YoussefMadian/safe-driving-system/Presentation/Photos/Slide1.JPG

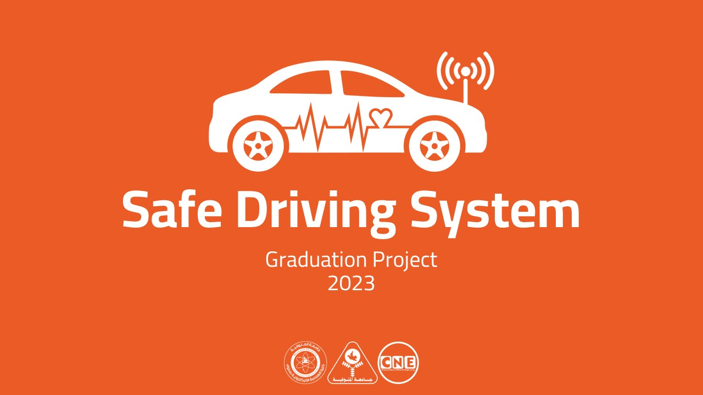
Presentation/Photos/Slide1.JPG
