YoussefMadian/safe-driving-system/Presentation/Photos/Slide2.JPG

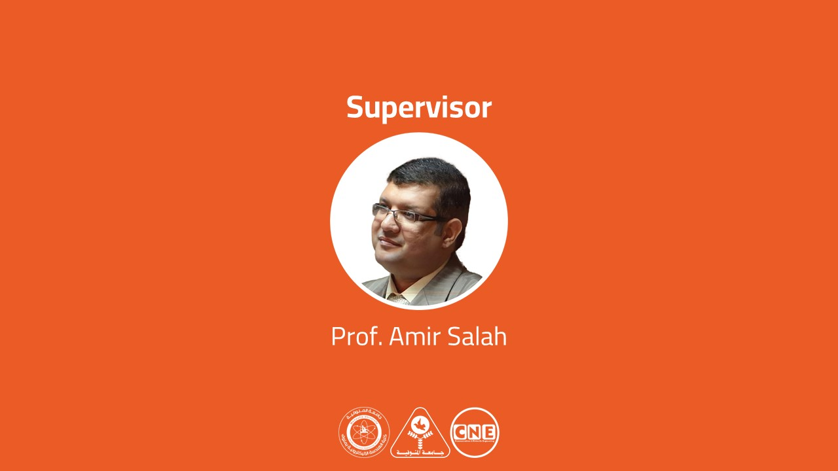
Presentation/Photos/Slide2.JPG
