YoussefMadian/safe-driving-system/Presentation/Photos/Slide3.JPG

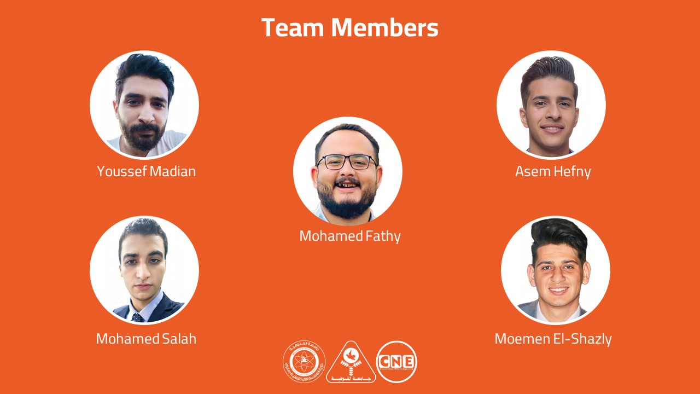
Presentation/Photos/Slide3.JPG
