YoussefMadian/safe-driving-system/Presentation/Photos/Slide4.JPG

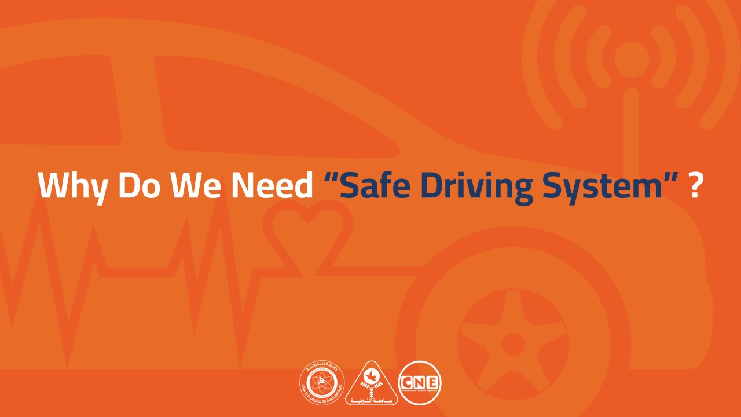
Presentation/Photos/Slide4.JPG
