YoussefMadian/safe-driving-system/Presentation/Photos/Slide5.JPG

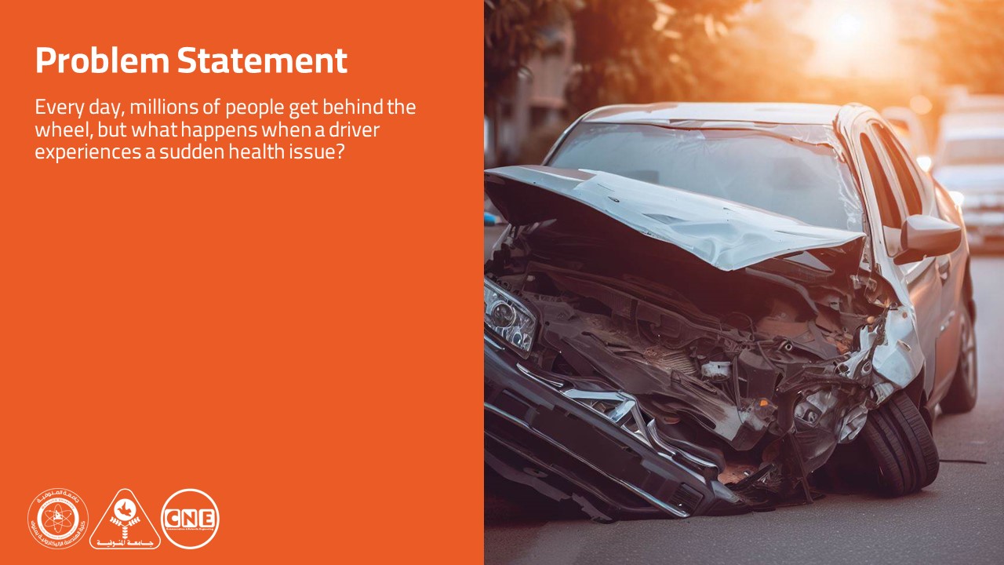
Presentation/Photos/Slide5.JPG
