YoussefMadian/safe-driving-system/Presentation/Photos/Slide6.JPG

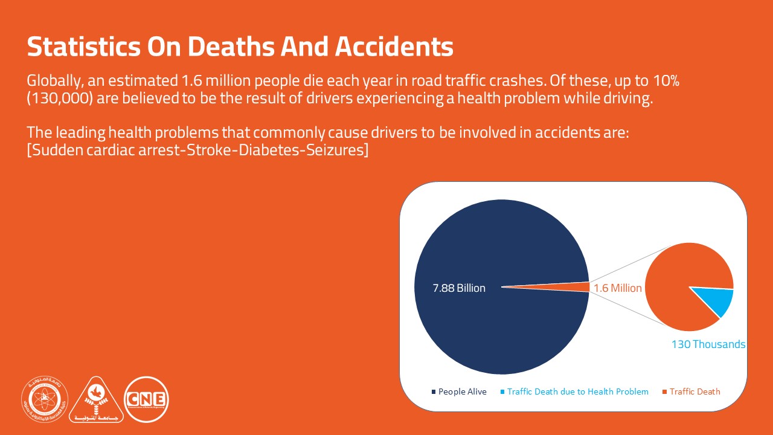
Presentation/Photos/Slide6.JPG
