YoussefMadian/safe-driving-system/Presentation/Photos/Slide7.JPG

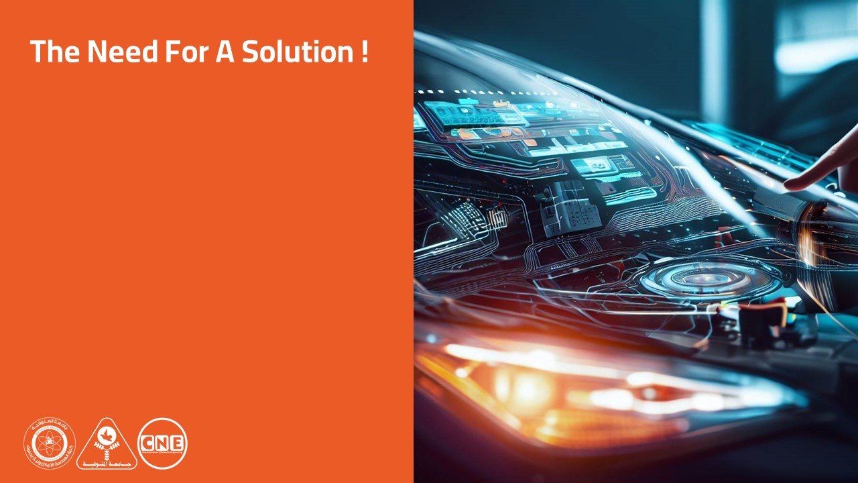
Presentation/Photos/Slide7.JPG
