YoussefMadian/safe-driving-system/Presentation/Photos/Slide8.JPG

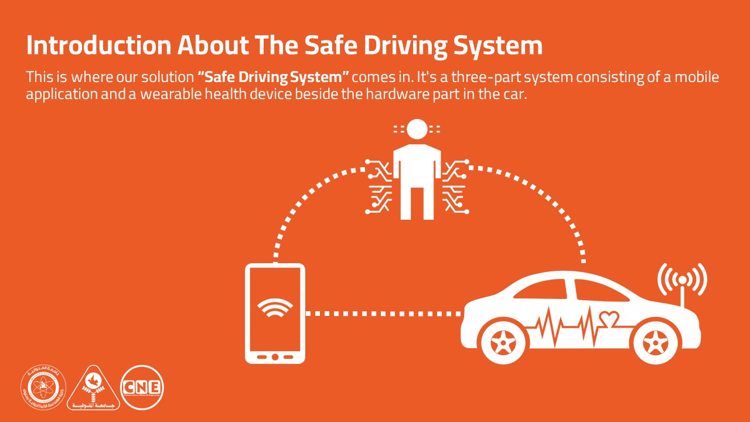
Presentation/Photos/Slide8.JPG
