YoussefMadian/safe-driving-system/Presentation/Photos/Slide9.JPG

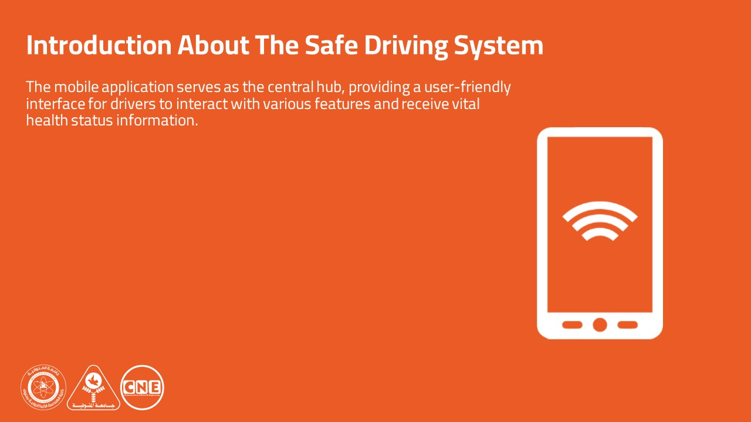
Presentation/Photos/Slide9.JPG
