YoussefMadian/safe-driving-system/Presentation/Photos/Slide10.JPG

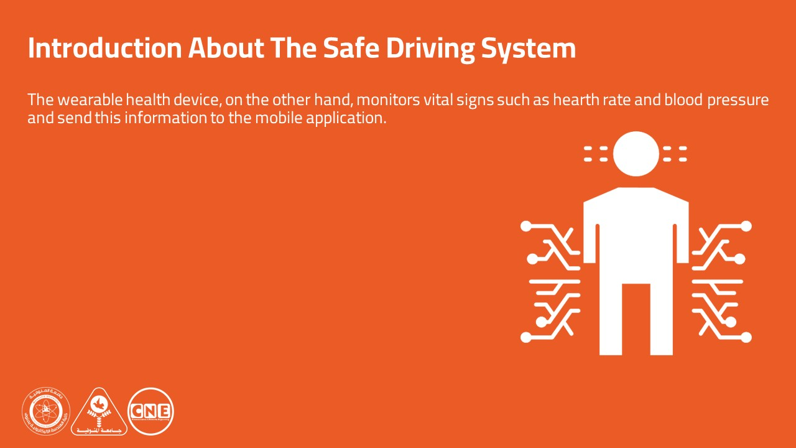
Presentation/Photos/Slide10.JPG
