YoussefMadian/safe-driving-system/Presentation/Photos/Slide11.JPG

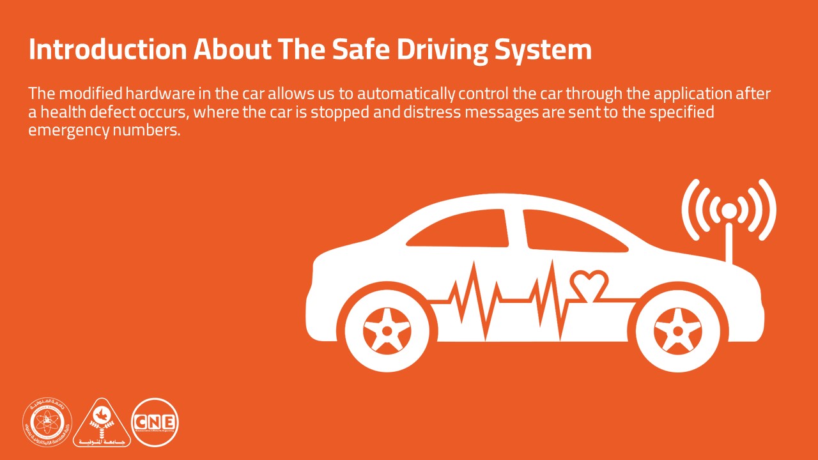
Presentation/Photos/Slide11.JPG
