YoussefMadian/safe-driving-system/Presentation/Photos/Slide12.JPG

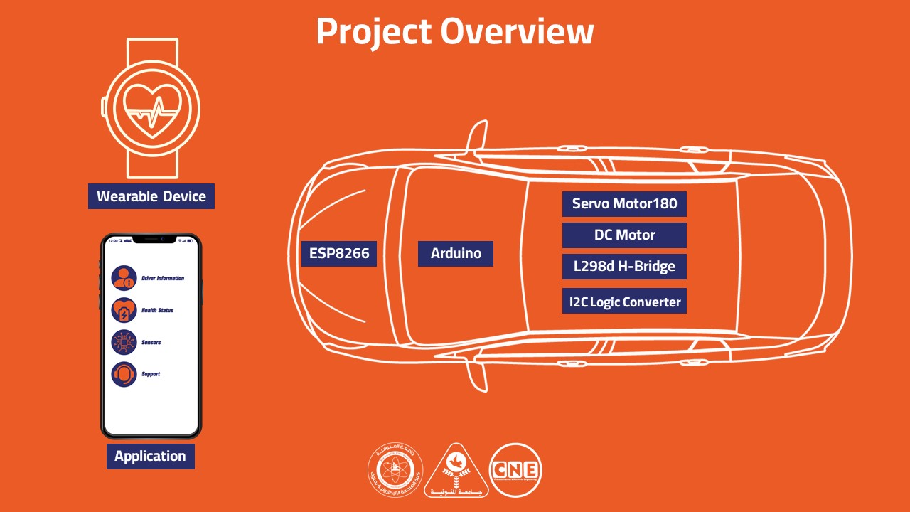
Presentation/Photos/Slide12.JPG
