YoussefMadian/safe-driving-system/Presentation/Photos/Slide13.JPG

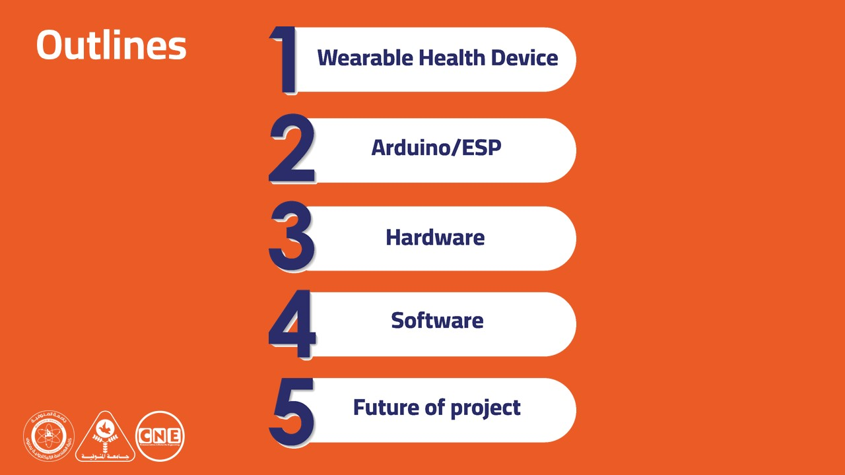
Presentation/Photos/Slide13.JPG
