YoussefMadian/safe-driving-system/Presentation/Photos/Slide14.JPG

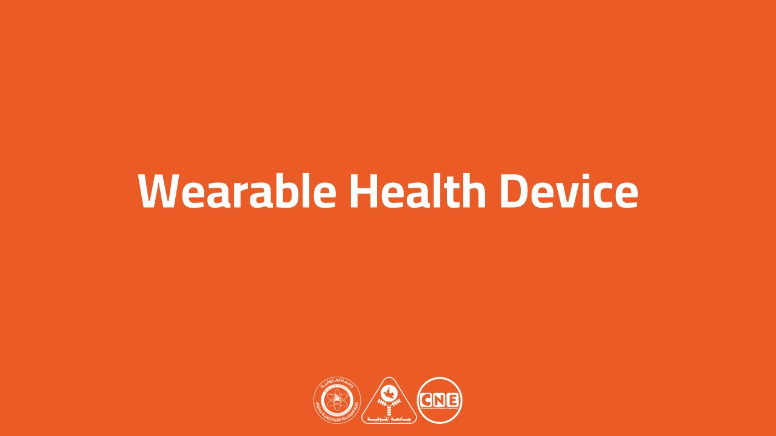
Presentation/Photos/Slide14.JPG
