YoussefMadian/safe-driving-system/Presentation/Photos/Slide15.JPG

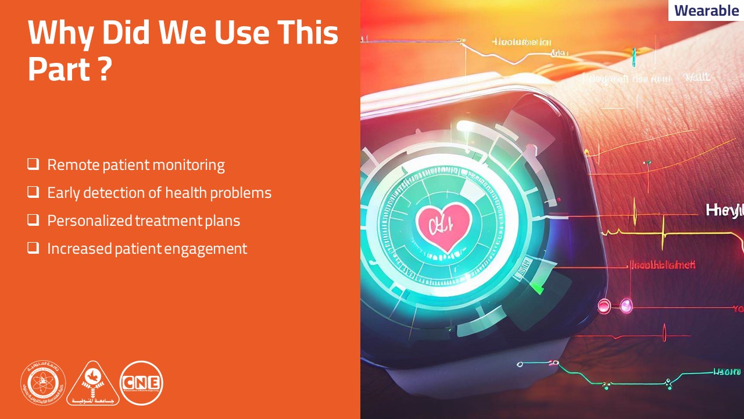
Presentation/Photos/Slide15.JPG
