YoussefMadian/safe-driving-system/Presentation/Photos/Slide16.JPG

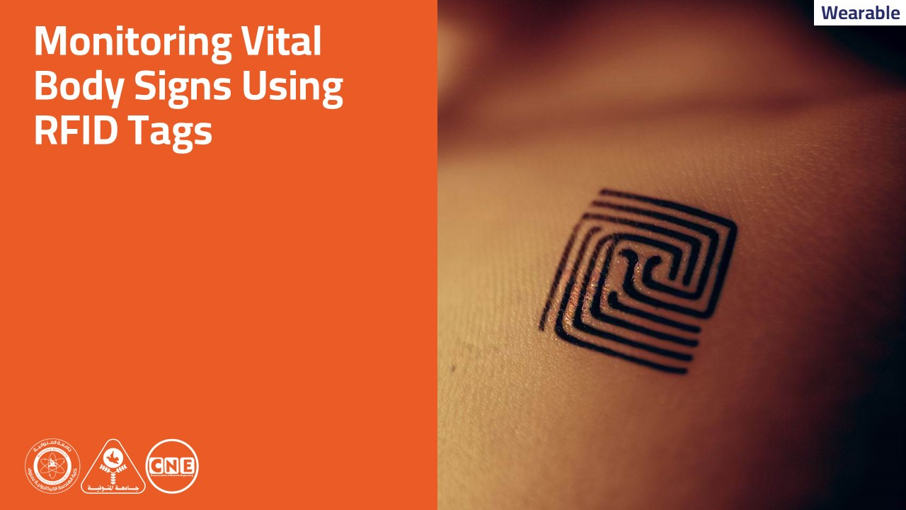
Presentation/Photos/Slide16.JPG
