YoussefMadian/safe-driving-system/Presentation/Photos/Slide18.JPG

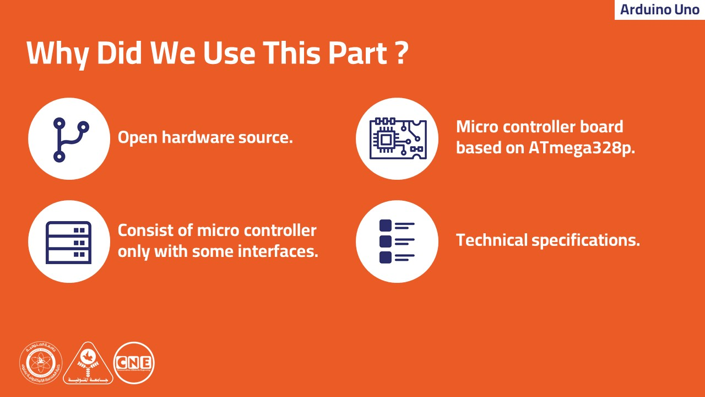
Presentation/Photos/Slide18.JPG
