YoussefMadian/safe-driving-system/Presentation/Photos/Slide19.JPG

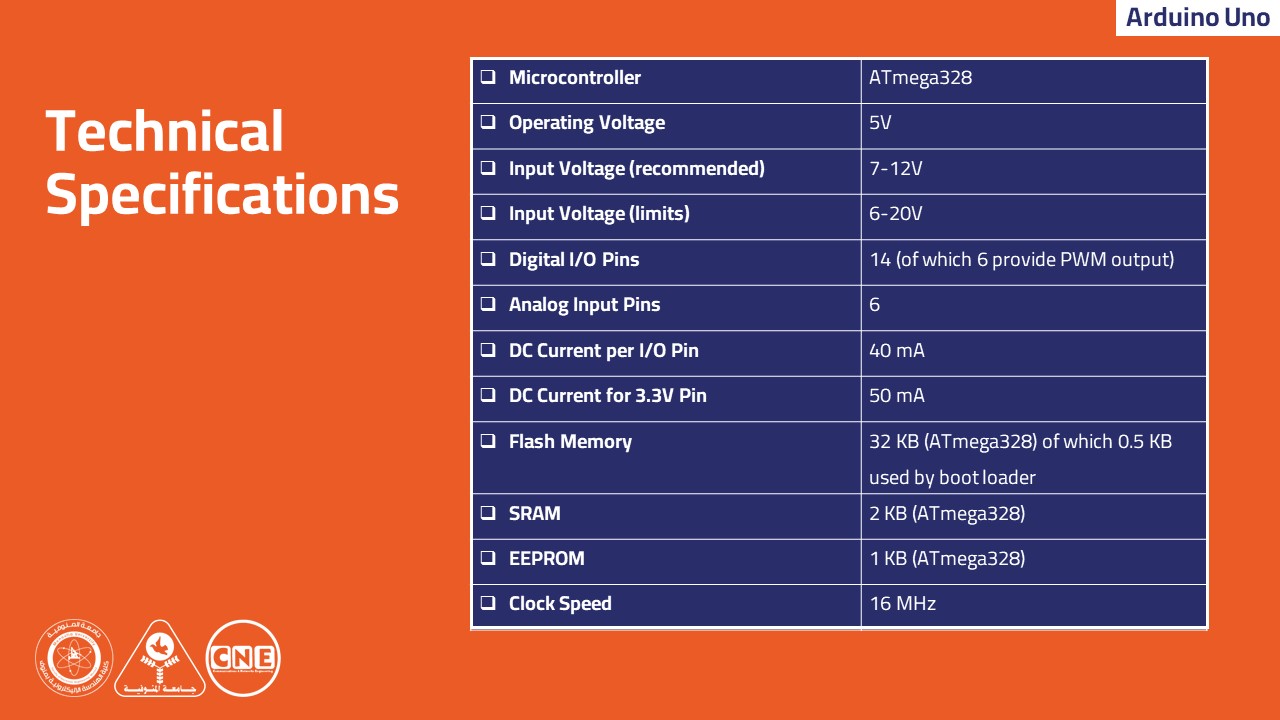
Presentation/Photos/Slide19.JPG
