YoussefMadian/safe-driving-system/Presentation/Photos/Slide20.JPG

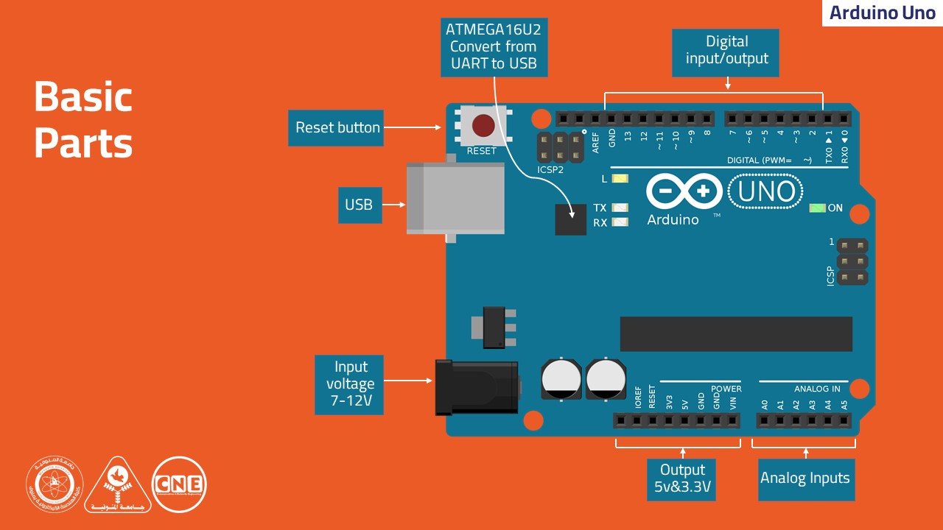
Presentation/Photos/Slide20.JPG
