YoussefMadian/safe-driving-system/Presentation/Photos/Slide22.JPG

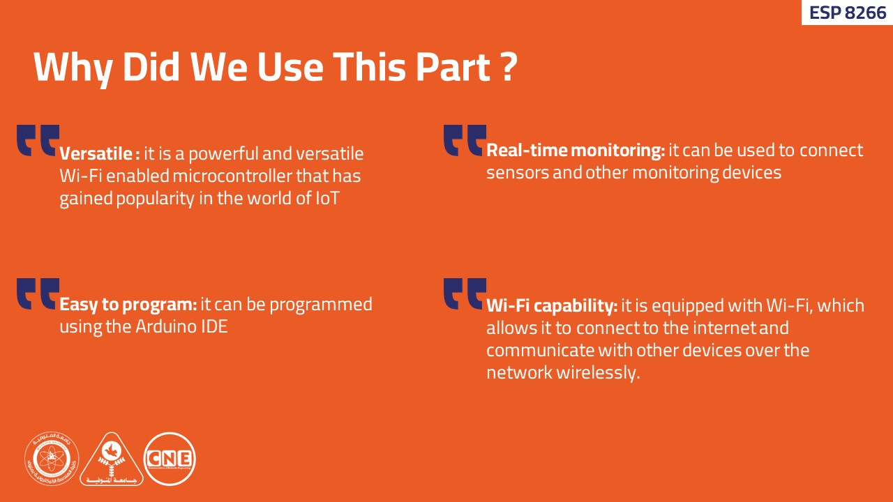
Presentation/Photos/Slide22.JPG
