YoussefMadian/safe-driving-system/Presentation/Photos/Slide23.JPG

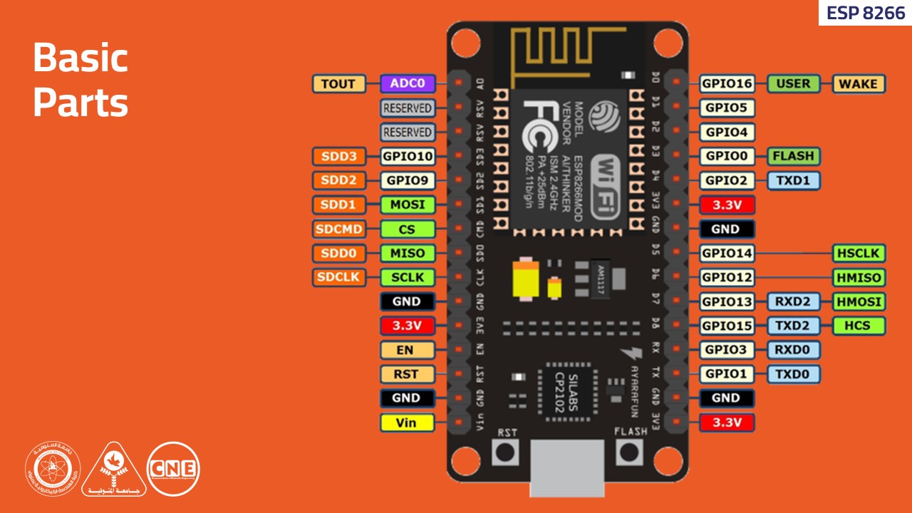
Presentation/Photos/Slide23.JPG
