YoussefMadian/safe-driving-system/Presentation/Photos/Slide24.JPG

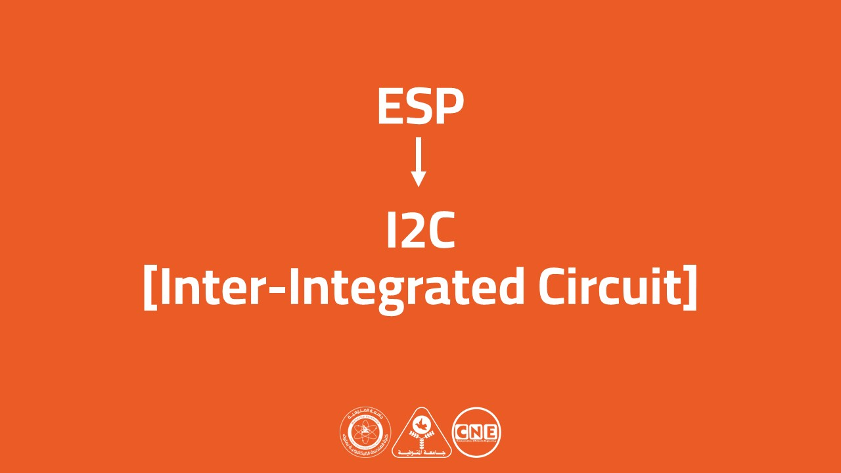
Presentation/Photos/Slide24.JPG
