YoussefMadian/safe-driving-system/Presentation/Photos/Slide25.JPG

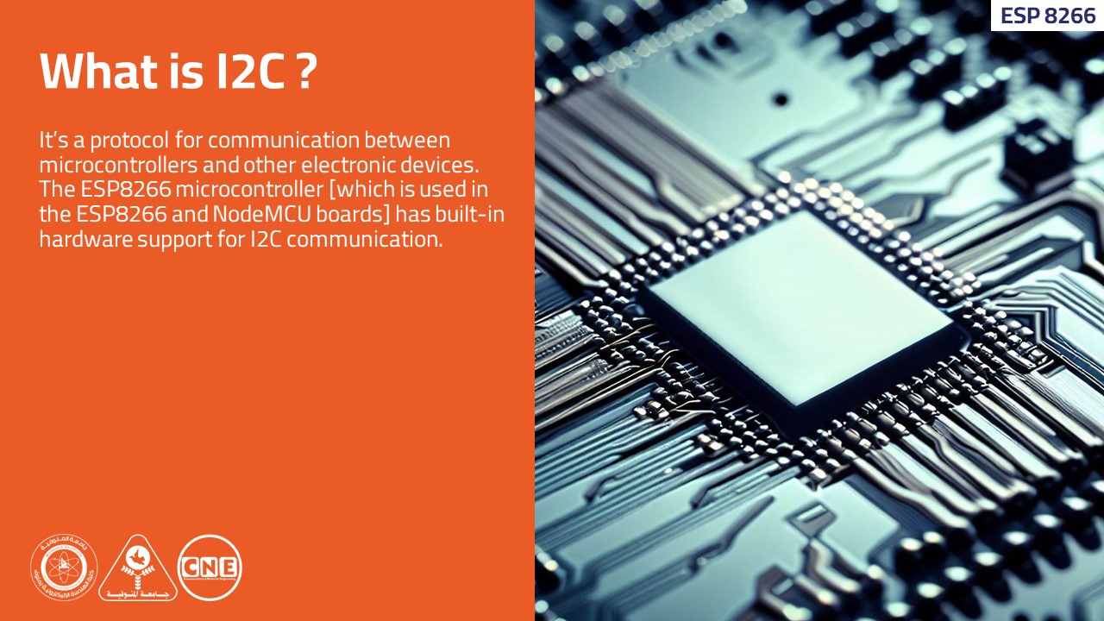
Presentation/Photos/Slide25.JPG
