YoussefMadian/safe-driving-system/Presentation/Photos/Slide26.JPG

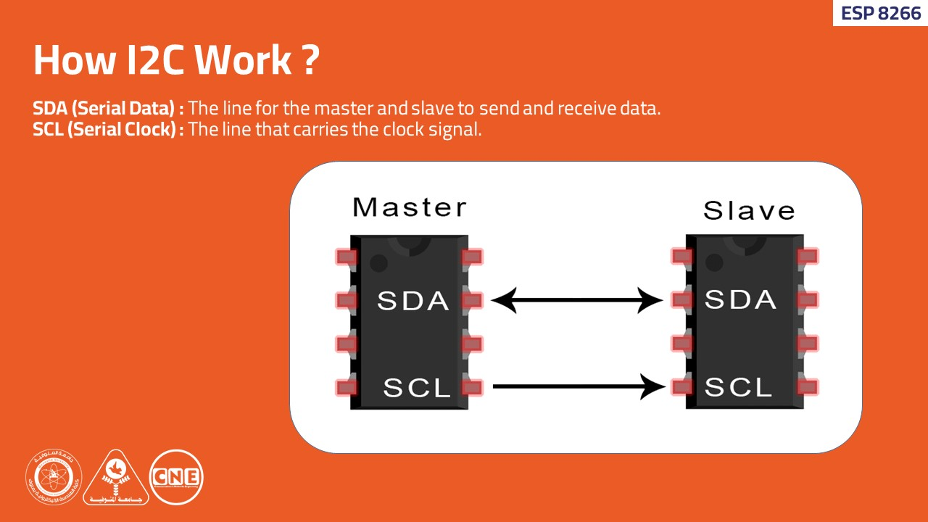
Presentation/Photos/Slide26.JPG
