YoussefMadian/safe-driving-system/Presentation/Photos/Slide27.JPG

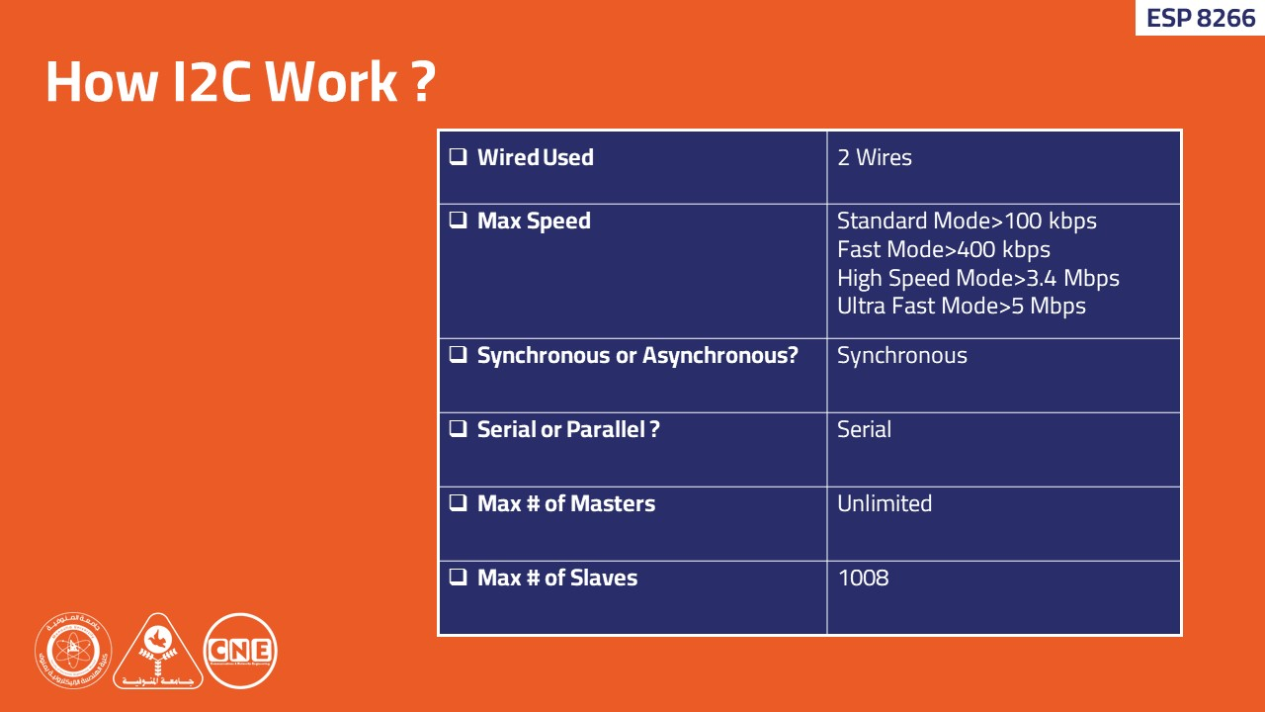
Presentation/Photos/Slide27.JPG
