YoussefMadian/safe-driving-system/Presentation/Photos/Slide28.JPG

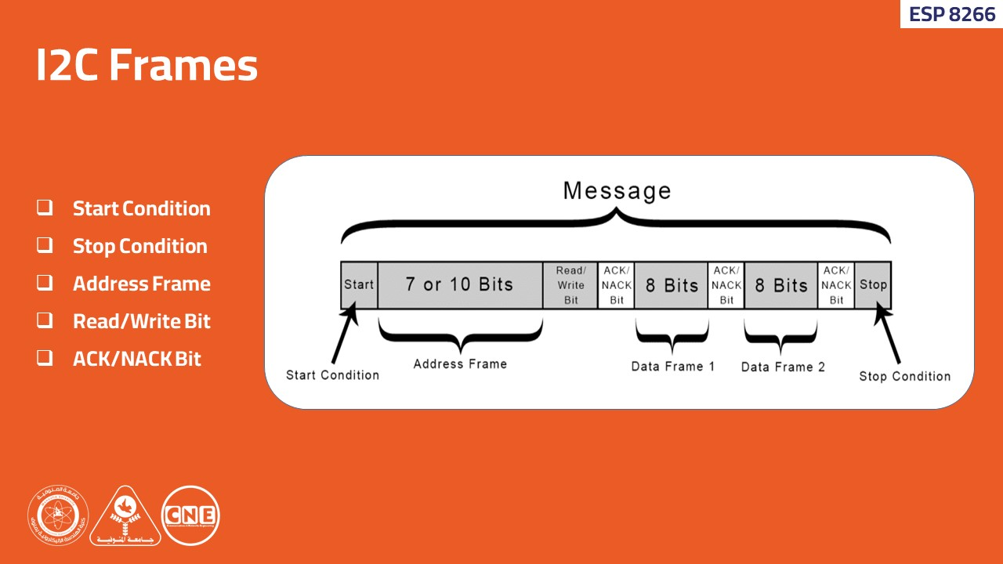
Presentation/Photos/Slide28.JPG
