YoussefMadian/safe-driving-system/Presentation/Photos/Slide29.JPG

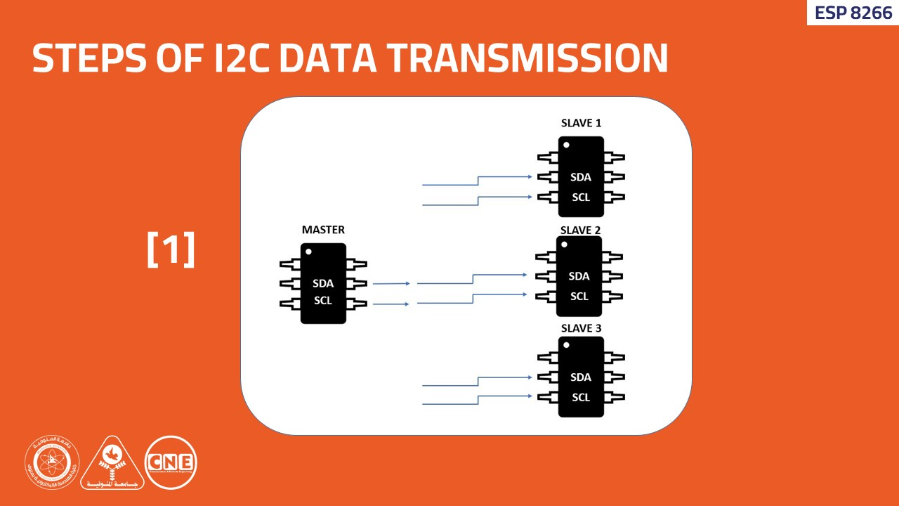
Presentation/Photos/Slide29.JPG
