YoussefMadian/safe-driving-system/Presentation/Photos/Slide33.JPG

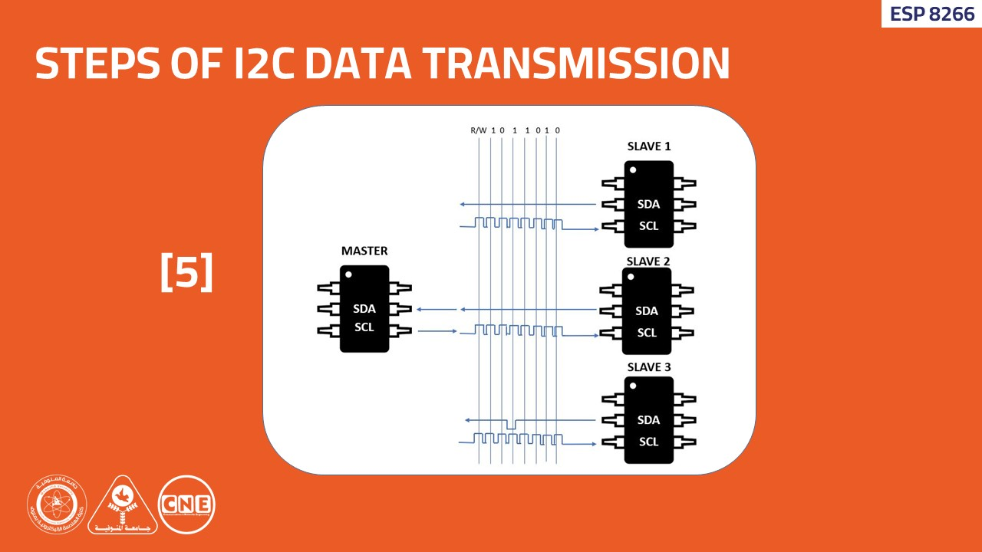
Presentation/Photos/Slide33.JPG
