YoussefMadian/safe-driving-system/Presentation/Photos/Slide35.JPG

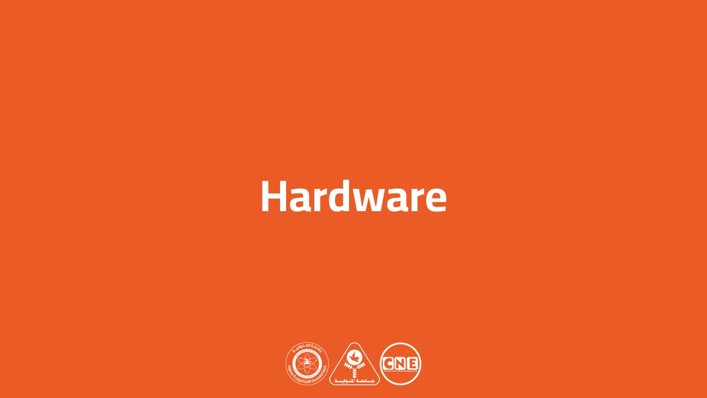
Presentation/Photos/Slide35.JPG
