YoussefMadian/safe-driving-system/Presentation/Photos/Slide36.JPG

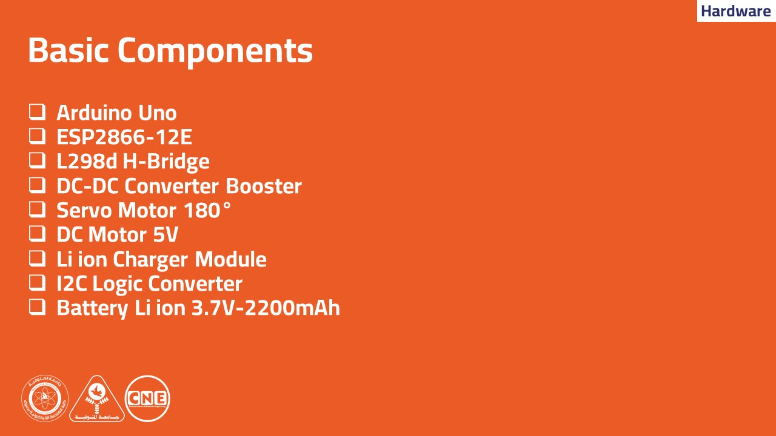
Presentation/Photos/Slide36.JPG
