YoussefMadian/safe-driving-system/Presentation/Photos/Slide37.JPG

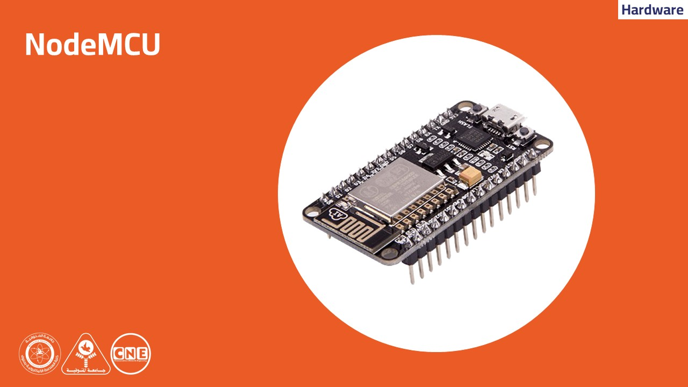
Presentation/Photos/Slide37.JPG
