YoussefMadian/safe-driving-system/Presentation/Photos/Slide38.JPG

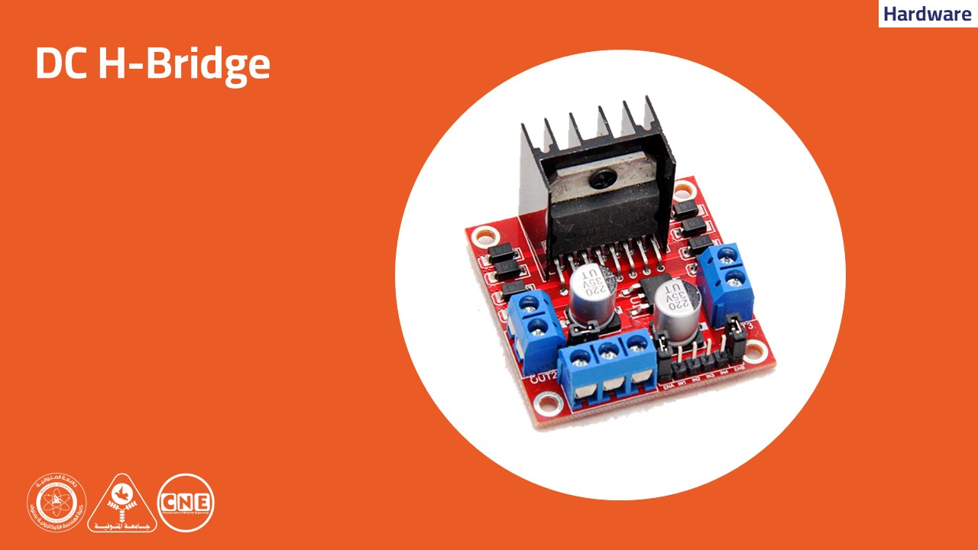
Presentation/Photos/Slide38.JPG
