YoussefMadian/safe-driving-system/Presentation/Photos/Slide39.JPG

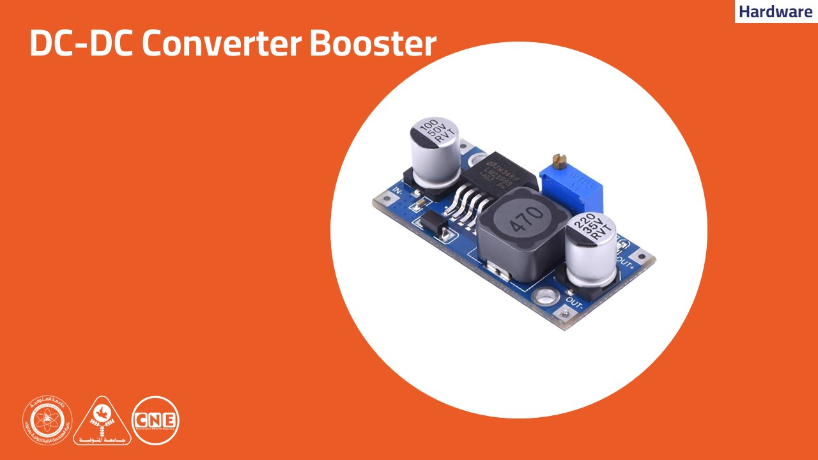
Presentation/Photos/Slide39.JPG
