YoussefMadian/safe-driving-system/Presentation/Photos/Slide40.JPG

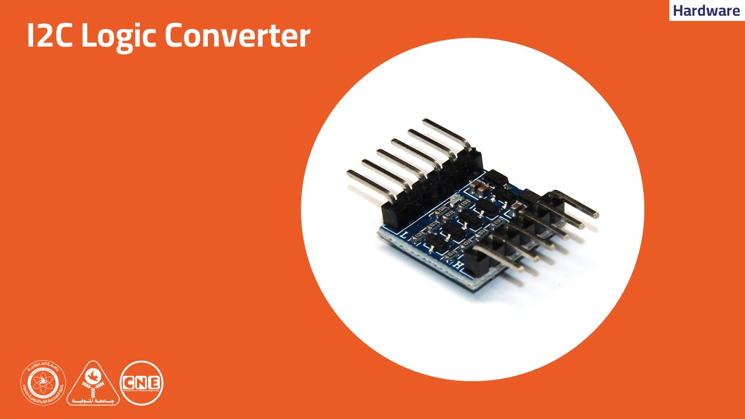
Presentation/Photos/Slide40.JPG
