YoussefMadian/safe-driving-system/Presentation/Photos/Slide42.JPG

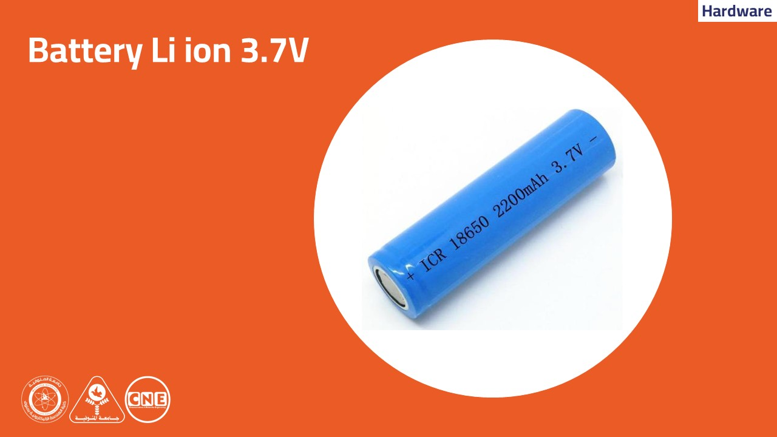
Presentation/Photos/Slide42.JPG
