YoussefMadian/safe-driving-system/Presentation/Photos/Slide43.JPG

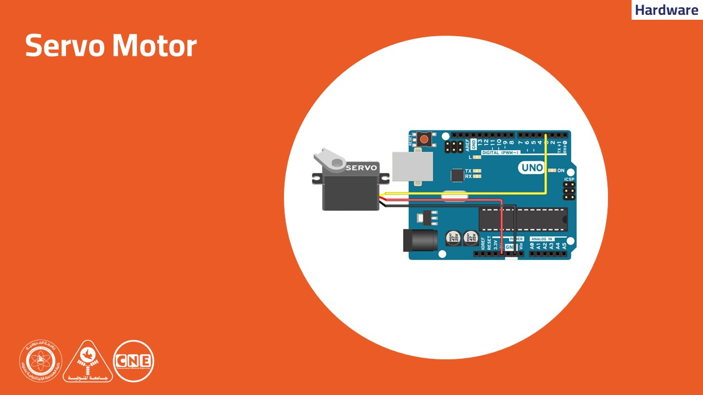
Presentation/Photos/Slide43.JPG
