YoussefMadian/safe-driving-system/Presentation/Photos/Slide44.JPG

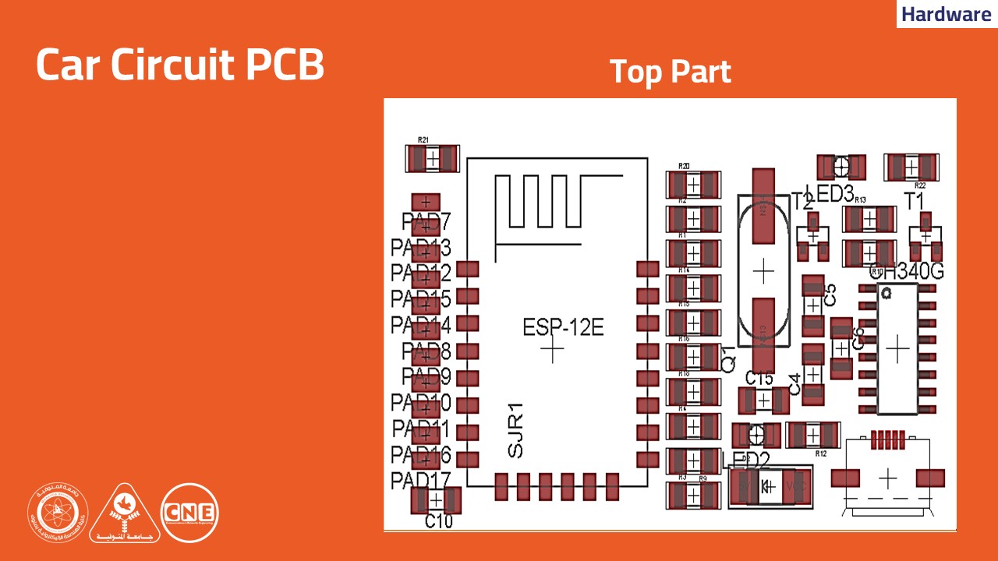
Presentation/Photos/Slide44.JPG
