YoussefMadian/safe-driving-system/Presentation/Photos/Slide45.JPG

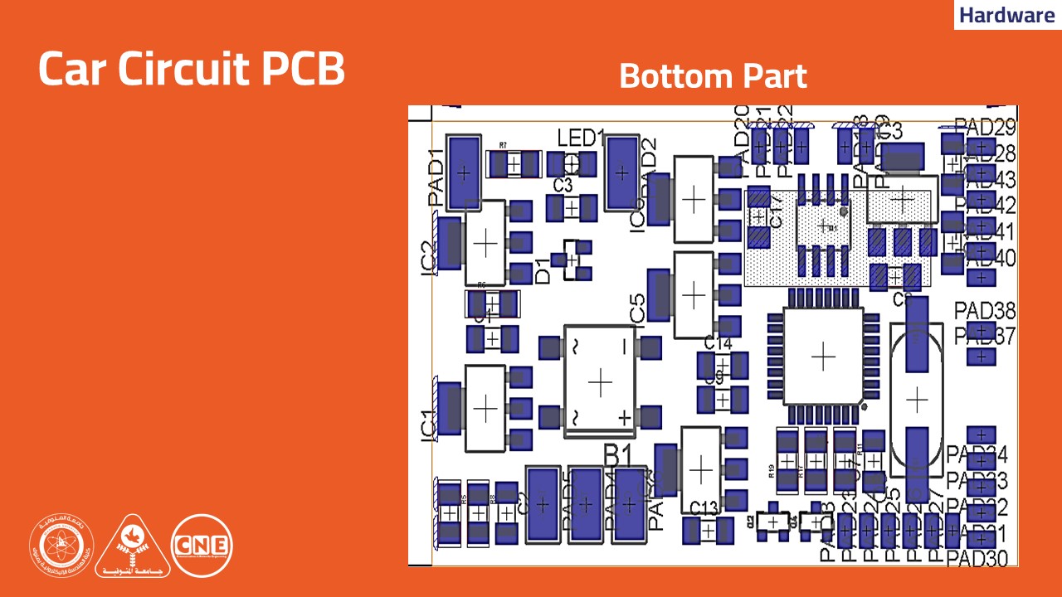
Presentation/Photos/Slide45.JPG
