YoussefMadian/safe-driving-system/Presentation/Photos/Slide47.JPG

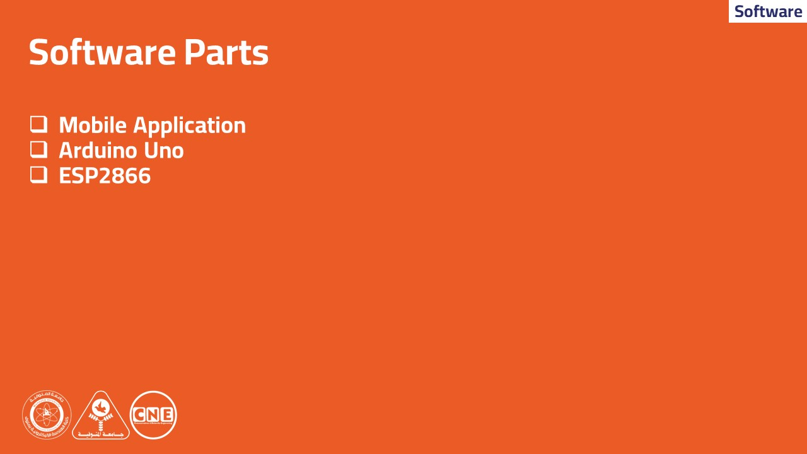
Presentation/Photos/Slide47.JPG
