YoussefMadian/safe-driving-system/Presentation/Photos/Slide48.JPG

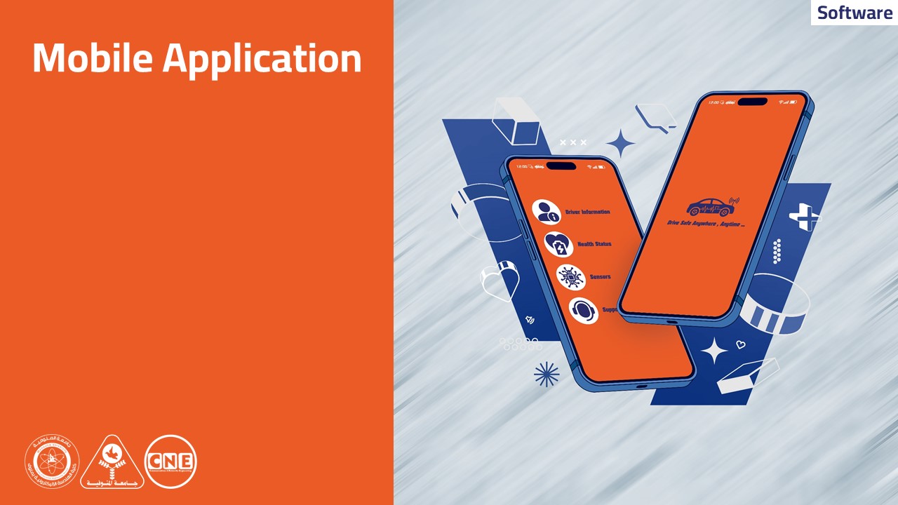
Presentation/Photos/Slide48.JPG
