YoussefMadian/safe-driving-system/Presentation/Photos/Slide49.JPG

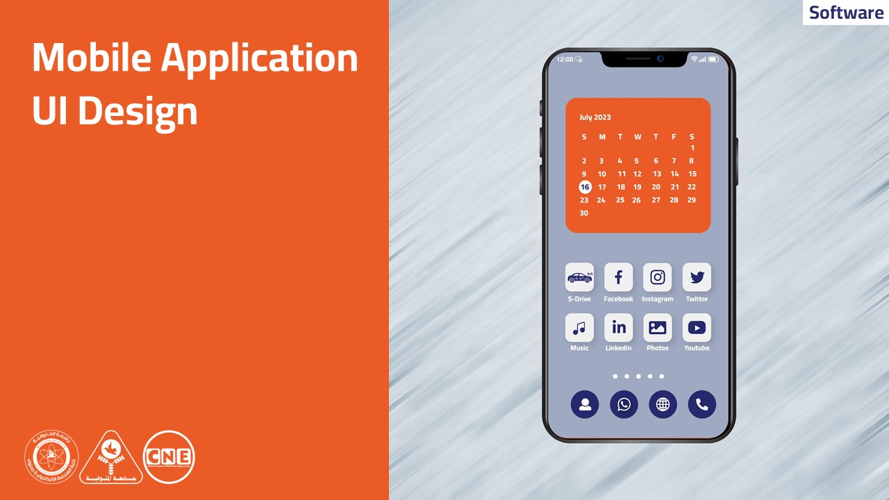
Presentation/Photos/Slide49.JPG
