YoussefMadian/safe-driving-system/Presentation/Photos/Slide56.JPG

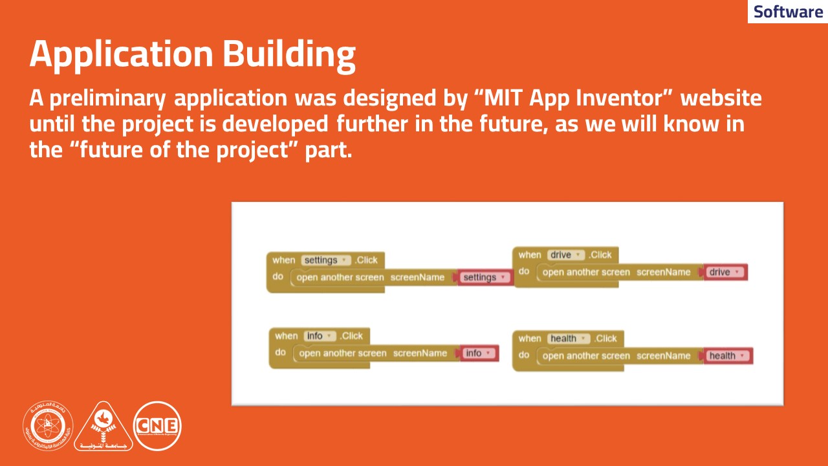
Presentation/Photos/Slide56.JPG
