YoussefMadian/safe-driving-system/Presentation/Photos/Slide57.JPG

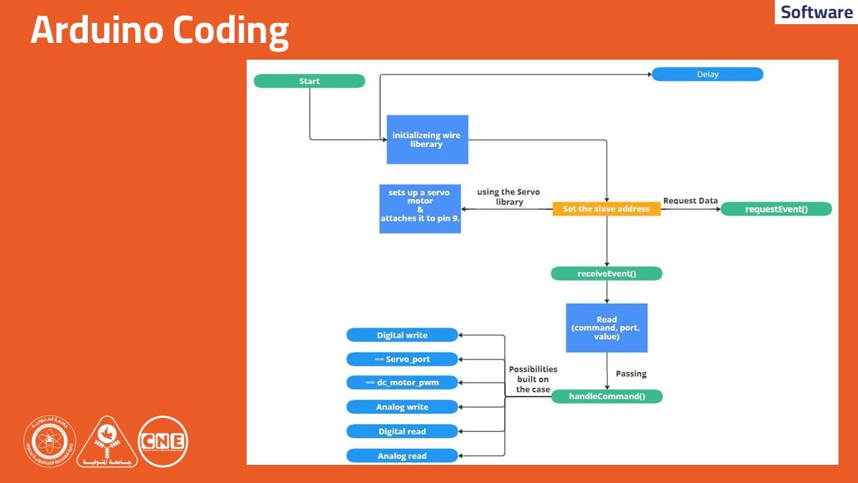
Presentation/Photos/Slide57.JPG
