YoussefMadian/safe-driving-system/Presentation/Photos/Slide58.JPG

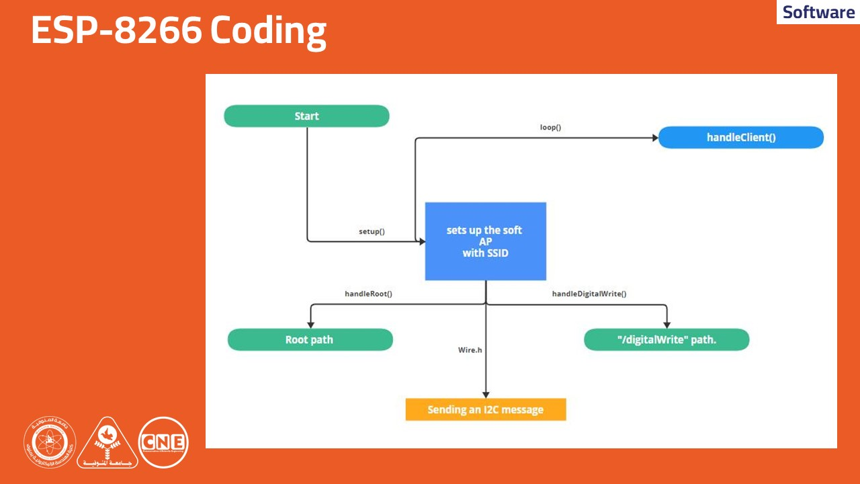
Presentation/Photos/Slide58.JPG
