YoussefMadian/safe-driving-system/Presentation/Photos/Slide59.JPG

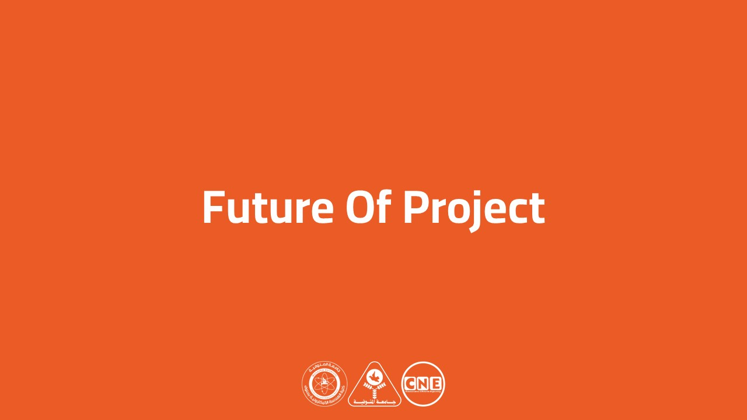
Presentation/Photos/Slide59.JPG
