YoussefMadian/safe-driving-system/Presentation/Photos/Slide60.JPG

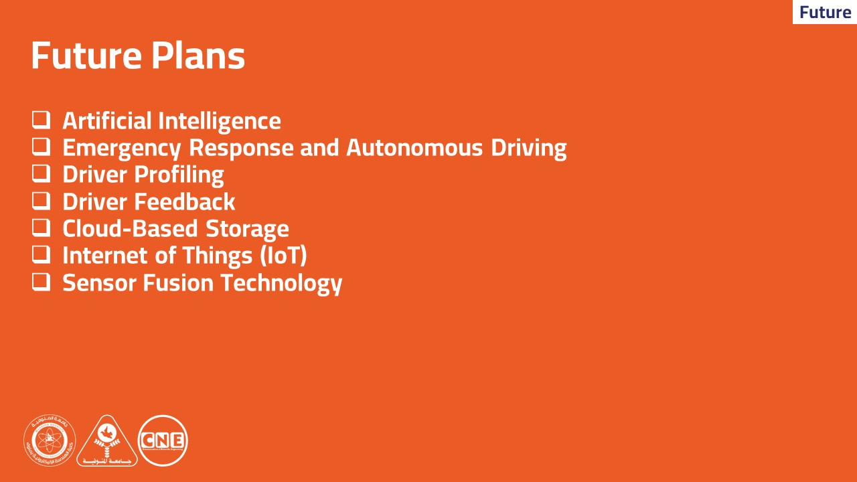
Presentation/Photos/Slide60.JPG
