YoussefMadian/safe-driving-system/Presentation/Photos/Slide61.JPG

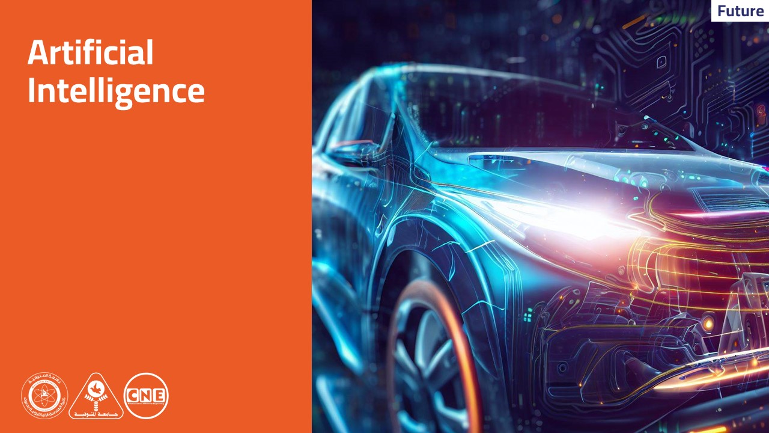
Presentation/Photos/Slide61.JPG
