YoussefMadian/safe-driving-system/Presentation/Photos/Slide63.JPG

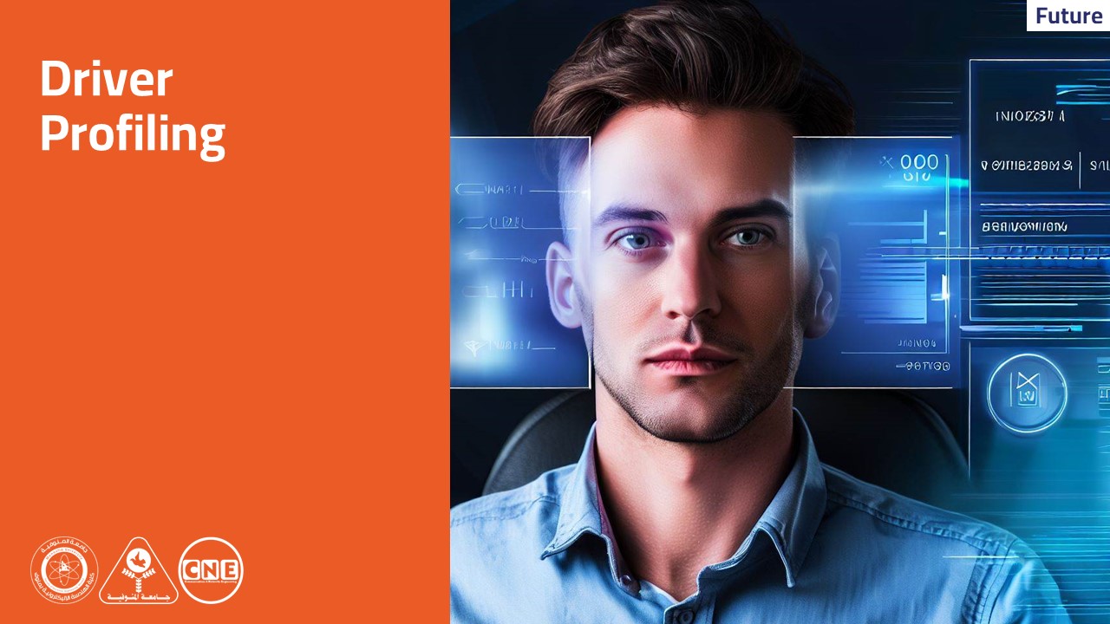
Presentation/Photos/Slide63.JPG
