YoussefMadian/safe-driving-system/Presentation/Photos/Slide64.JPG

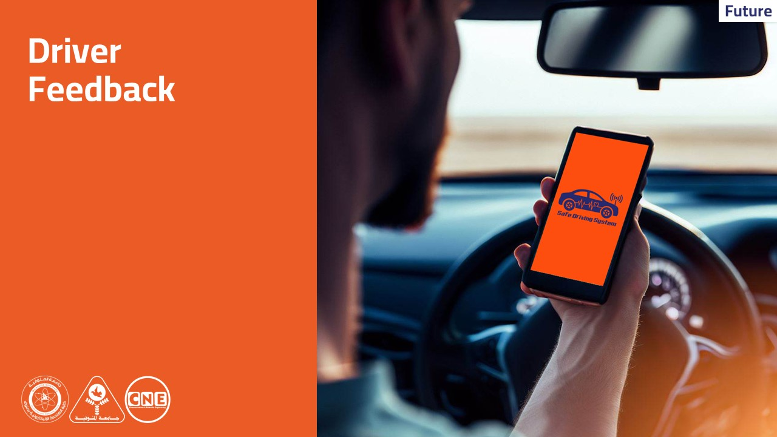
Presentation/Photos/Slide64.JPG
