YoussefMadian/safe-driving-system/Presentation/Photos/Slide65.JPG

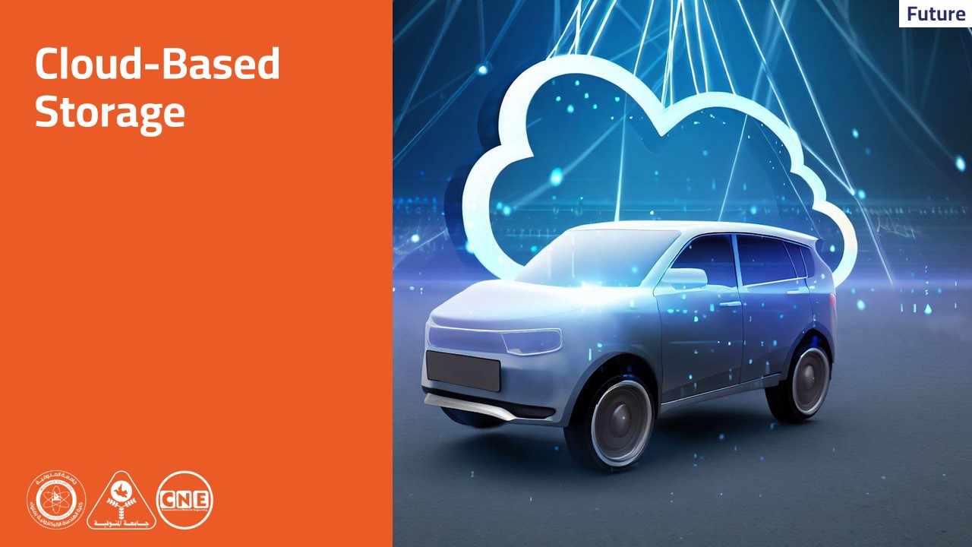
Presentation/Photos/Slide65.JPG
