YoussefMadian/safe-driving-system/Presentation/Photos/Slide66.JPG

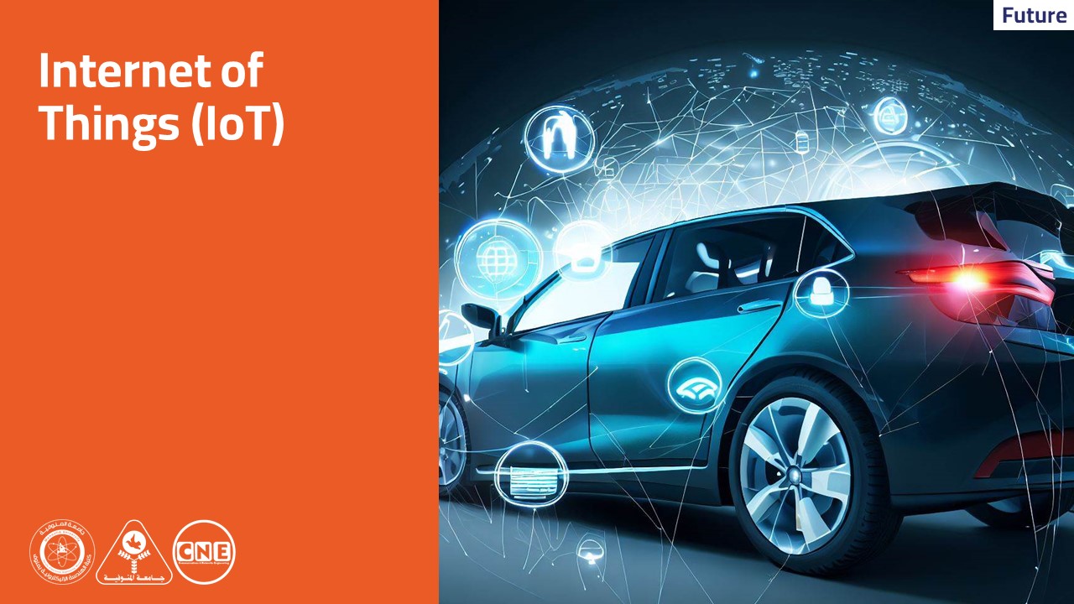
Presentation/Photos/Slide66.JPG
