YoussefMadian/safe-driving-system/Presentation/Photos/Slide67.JPG

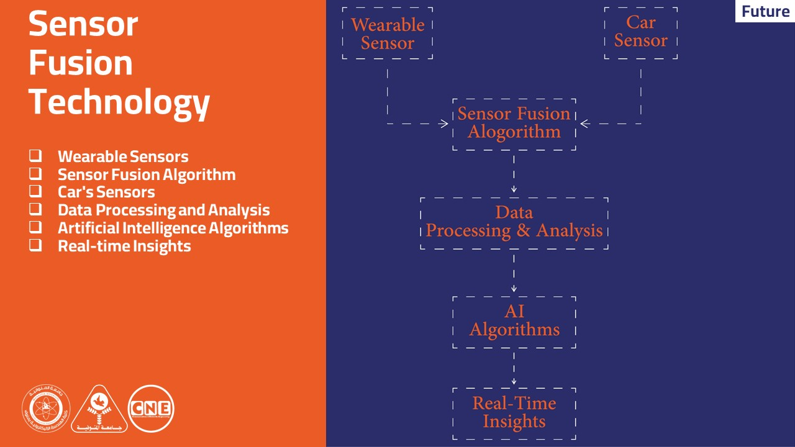
Presentation/Photos/Slide67.JPG
