YoussefMadian/safe-driving-system/Presentation/Photos/Slide68.JPG

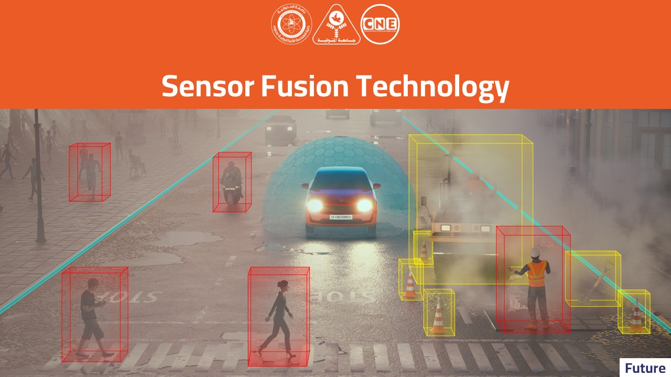
Presentation/Photos/Slide68.JPG
