YoussefMadian/safe-driving-system/Prints/Flyers/face.jpg

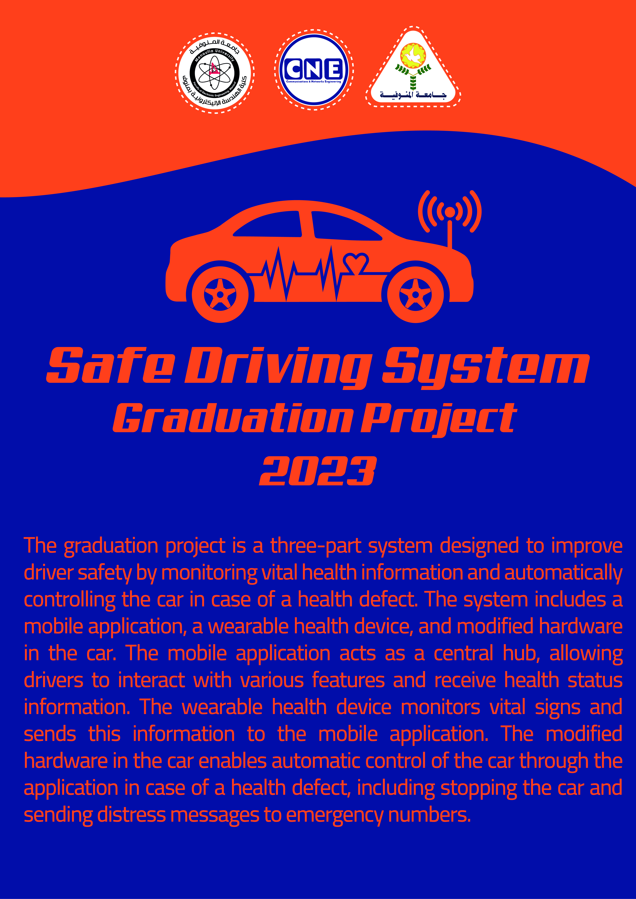
Prints/Flyers/face.jpg
